Avtom/GRAM-PRISM/Arcade  v1/art/back.png

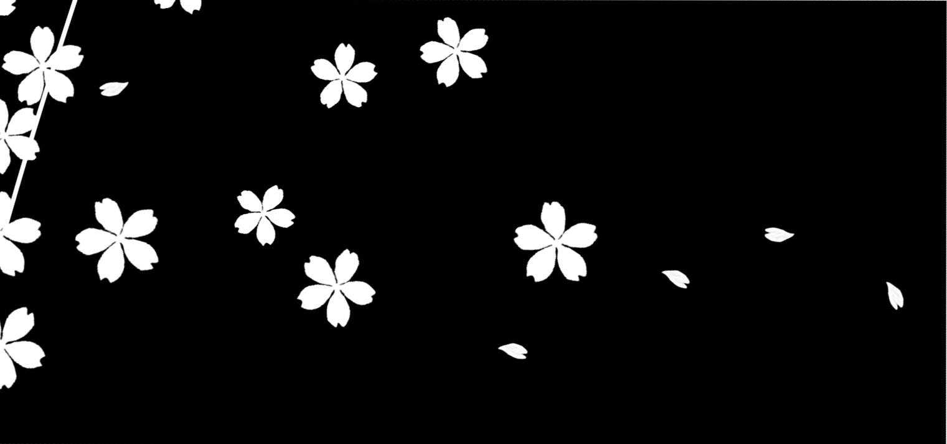
Arcade v1/art/back.png
