Avtom/GRAM-PRISM/Arcade  v1/art/front.png

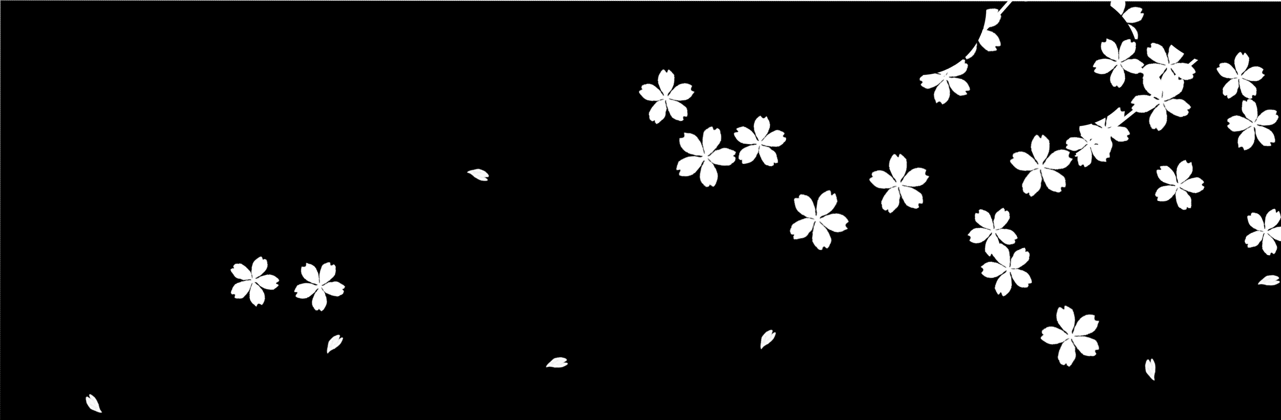
Arcade v1/art/front.png
