Avtom/GRAM-PRISM/Arcade  v1/art/left.png

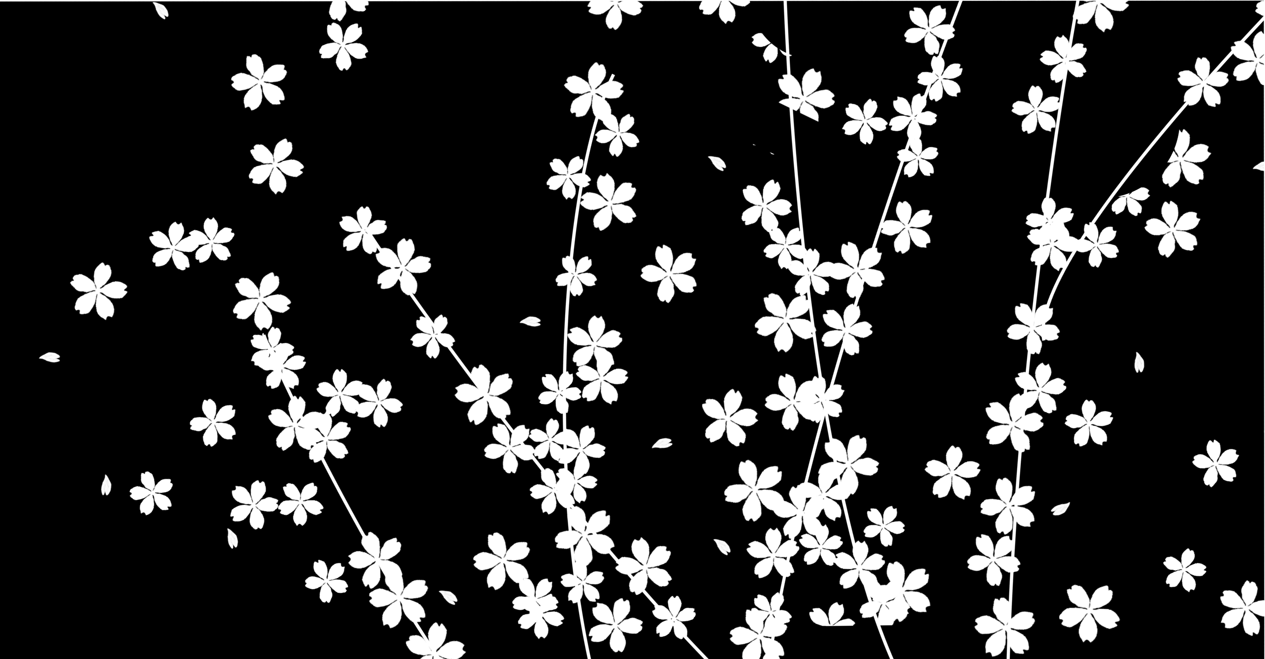
Arcade v1/art/left.png
