Avtom/GRAM-PRISM/Arcade  v1/art/right.png

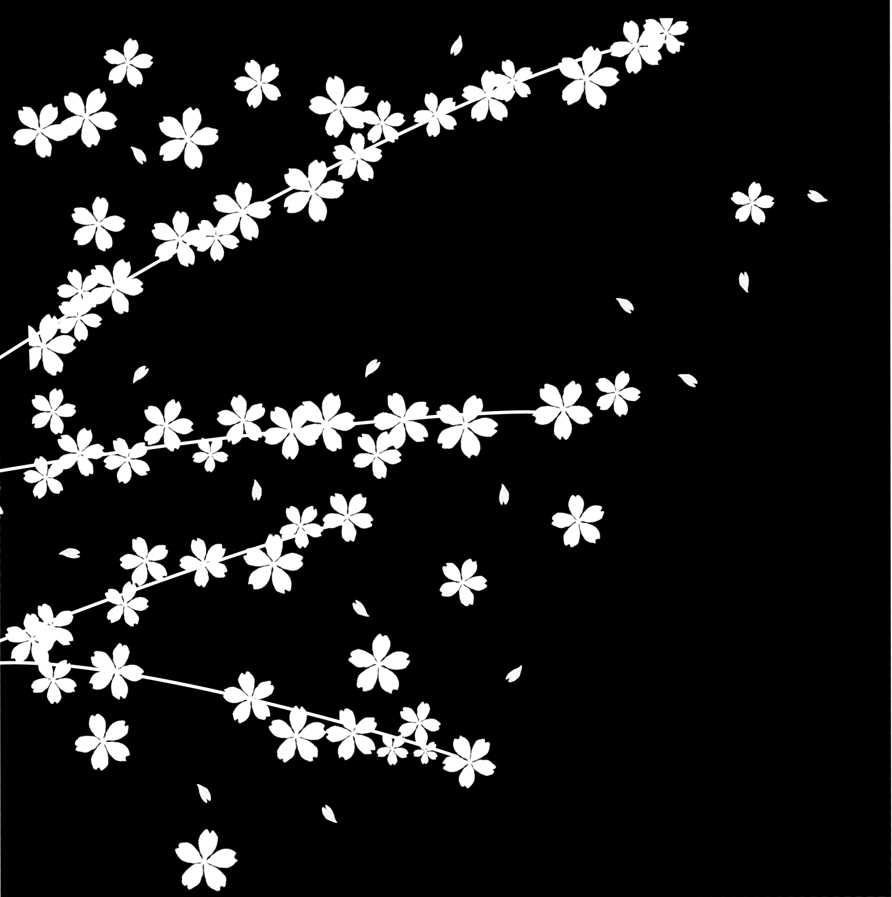
Arcade v1/art/right.png
