Avtom/GRAM-PRISM/Arcade  v1/documentation/arcade-2.jpg

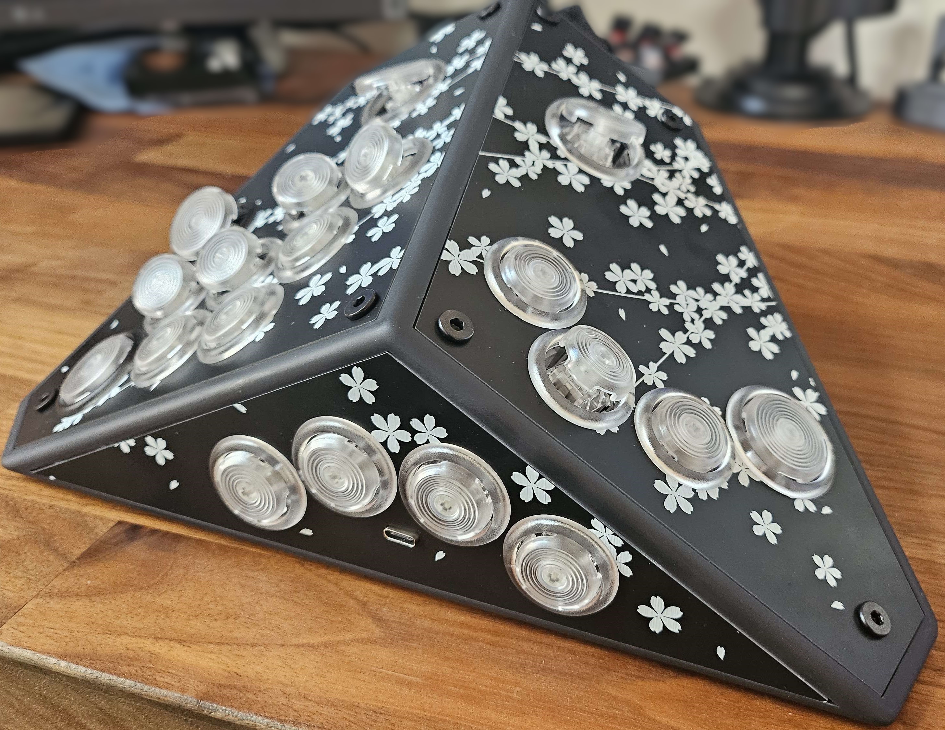
Arcade v1/documentation/arcade-2.jpg
