Avtom/GRAM-PRISM/Arcade  v1/documentation/arcade-3.jpg

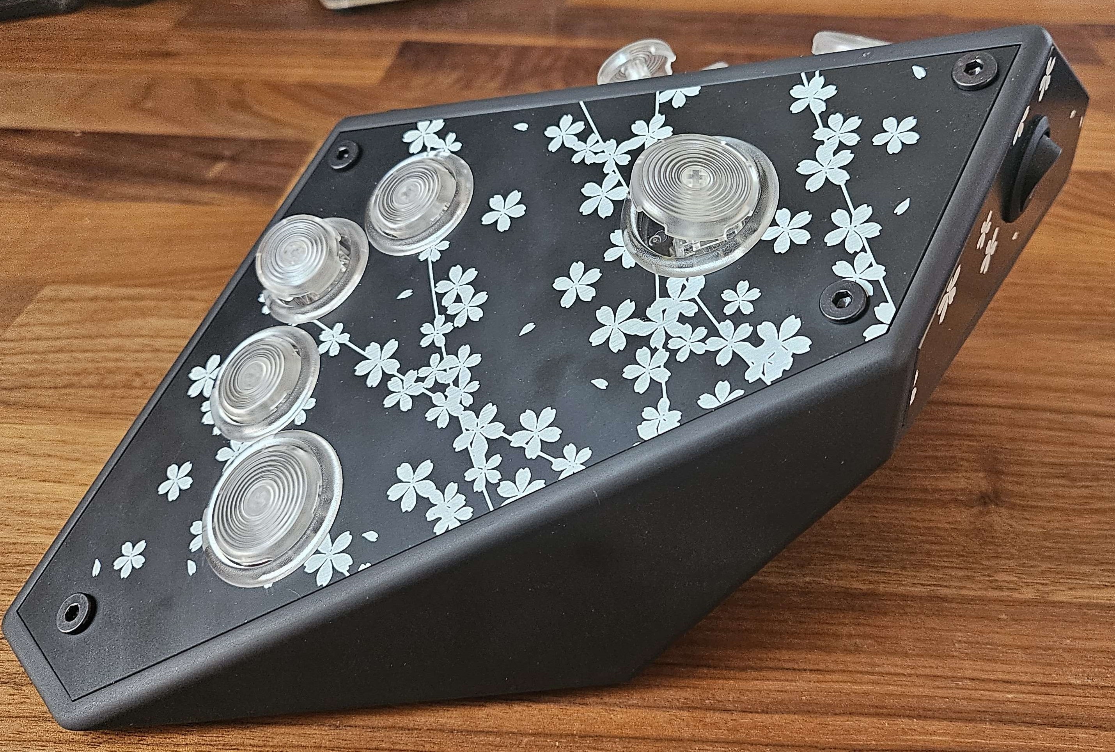
Arcade v1/documentation/arcade-3.jpg
