Avtom/GRAM-PRISM/Arcade  v1/documentation/arcade-4.jpg

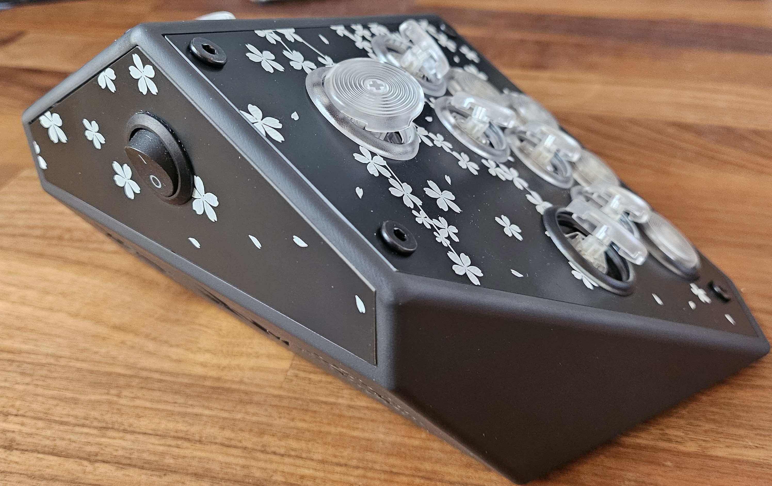
Arcade v1/documentation/arcade-4.jpg
