Avtom/GRAM-PRISM/Arcade  v1/documentation/arcade-5.jpg

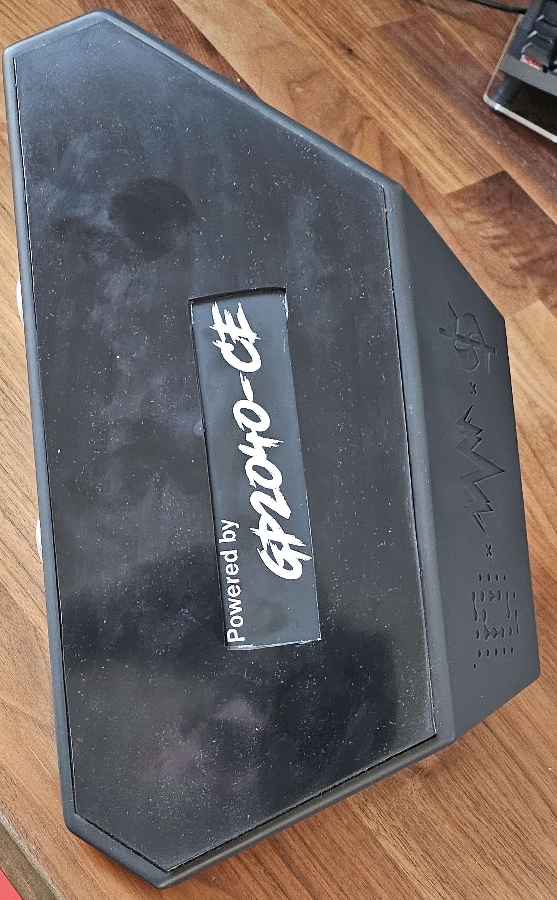
Arcade v1/documentation/arcade-5.jpg
