Avtom/GRAM-PRISM/Arcade  v1/documentation/arcade-6.jpg

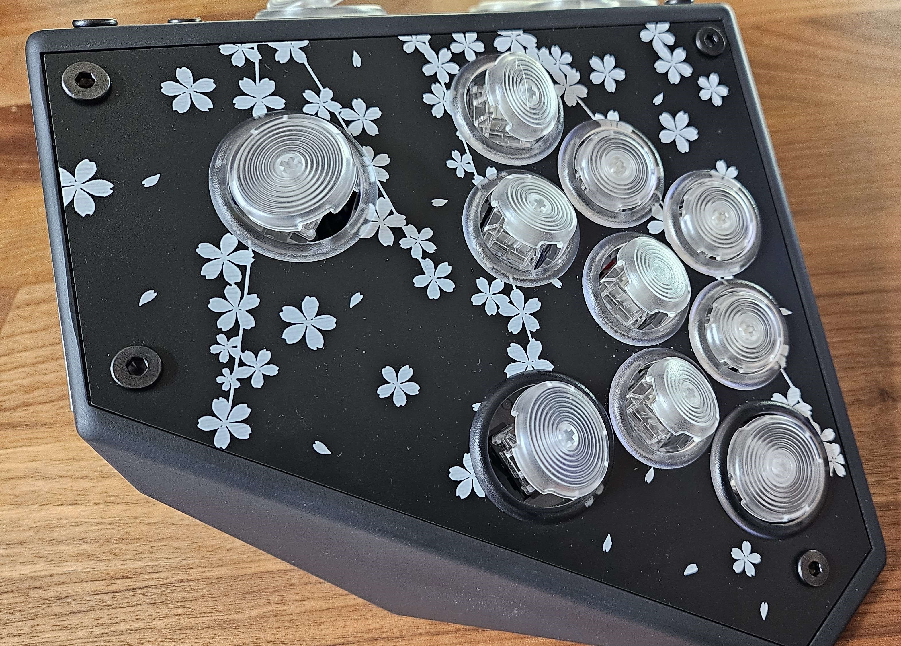
Arcade v1/documentation/arcade-6.jpg
