Avtom/GRAM-PRISM/Arcade  v1/documentation/arcade-7.jpg

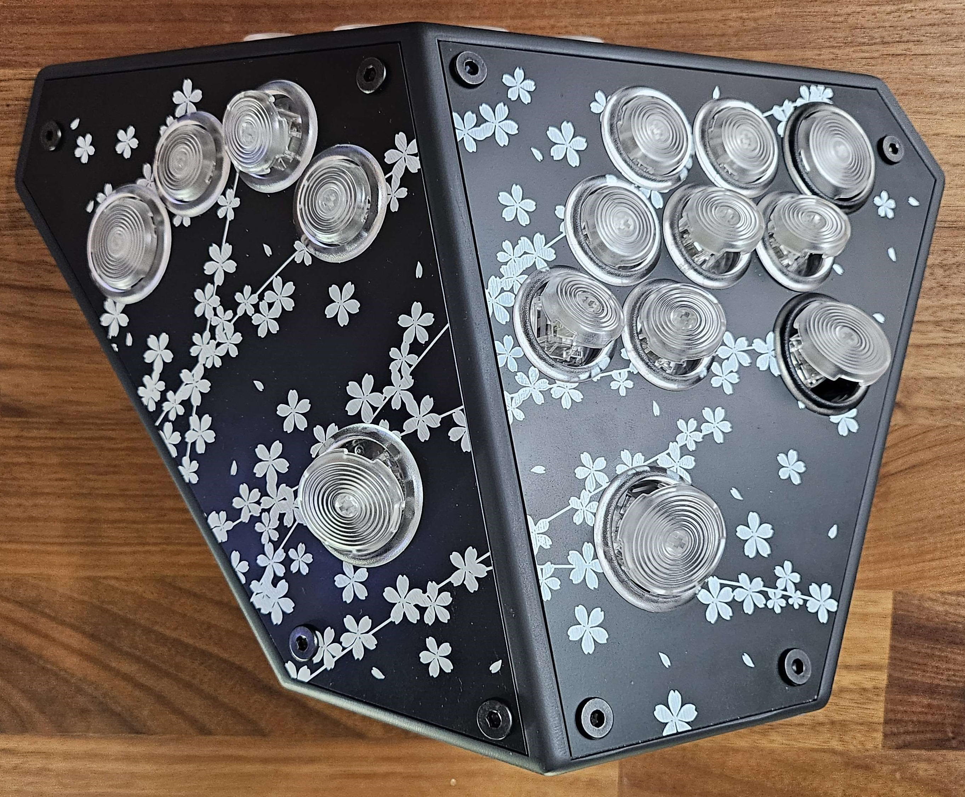
Arcade v1/documentation/arcade-7.jpg
