Avtom/GRAM-PRISM/Arcade  v1/documentation/arcade-notilters.jpg

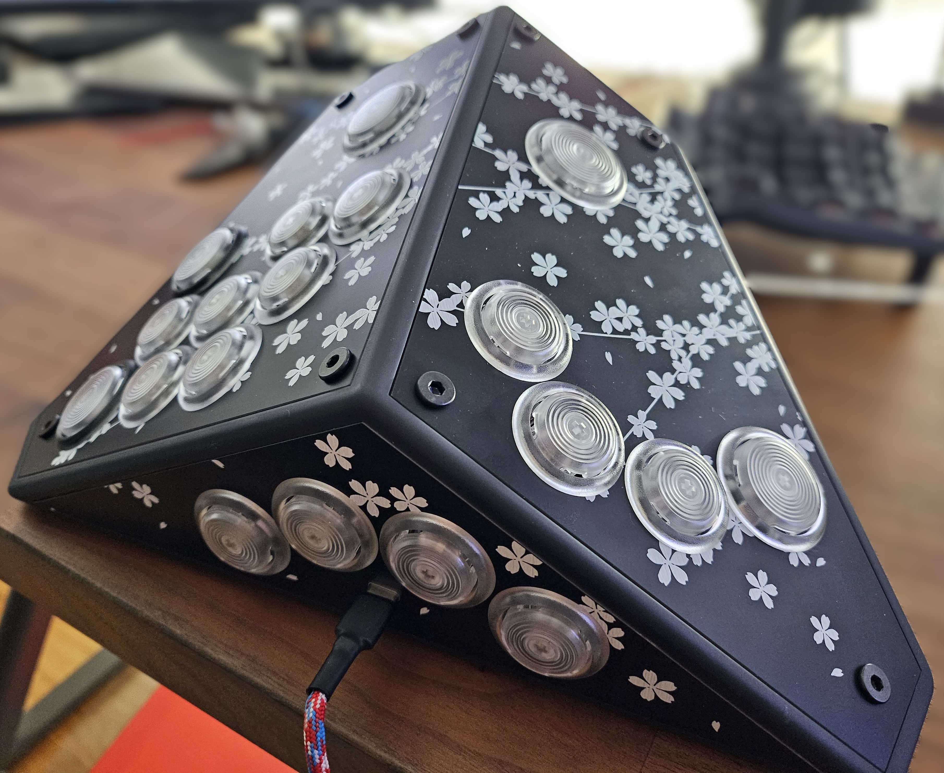
Arcade v1/documentation/arcade-notilters.jpg
