Avtom/GRAM-PRISM/Arcade  v1/documentation/without-button-2.jpg

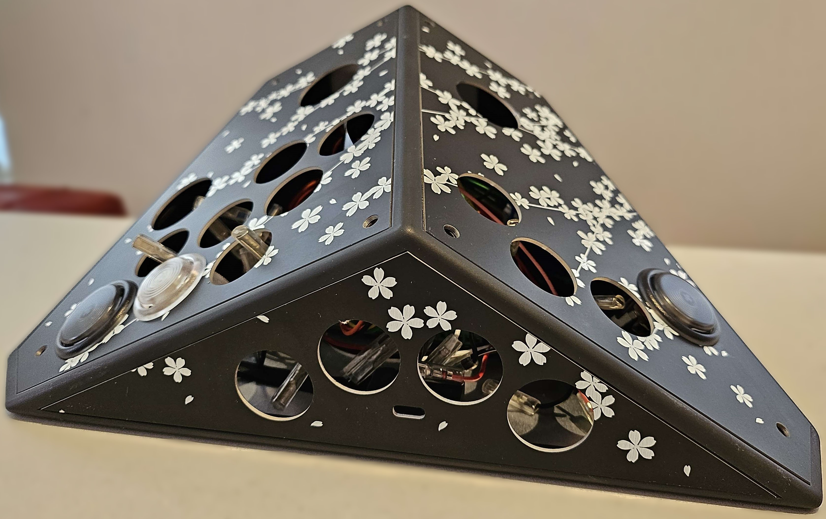
Arcade v1/documentation/without-button-2.jpg
