Avtom/GRAM-PRISM/Arcade  v1/stl/stl 2mm thick/right panel no aux buttons alt version v1.stl

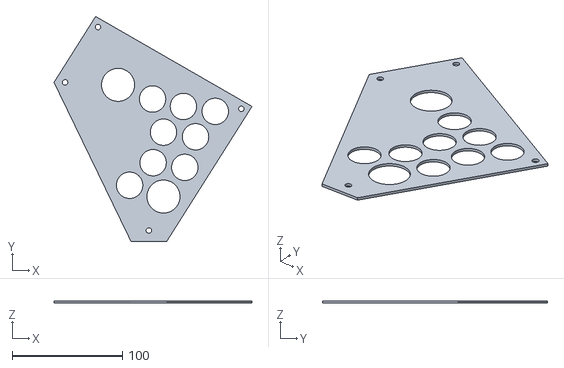
[picture p54: CAD file, 2024-02-25]
Arcade v1/stl/stl 2mm thick/right panel no aux buttons alt version v1.stl
179.7 x 204.3 x 2.00
