Avtom/GRAM-PRISM/Arcade  v1/dxf/left panel 16mm aux buttons.dxf

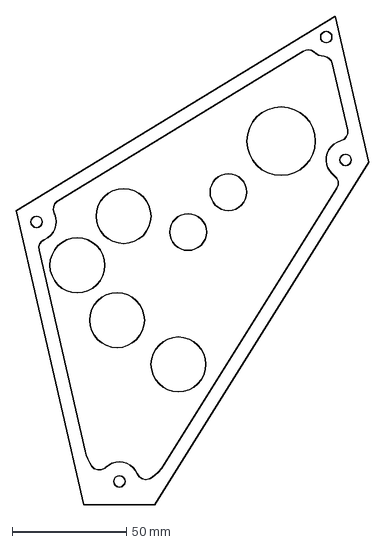
[picture p55: CAD file, 2024-02-10]
Arcade v1/dxf/left panel 16mm aux buttons.dxf
153.9 x 213.6 mm
