Avtom/GRAM-PRISM/Arcade  v1/stl/stl 2mm thick/bottom v1.stl

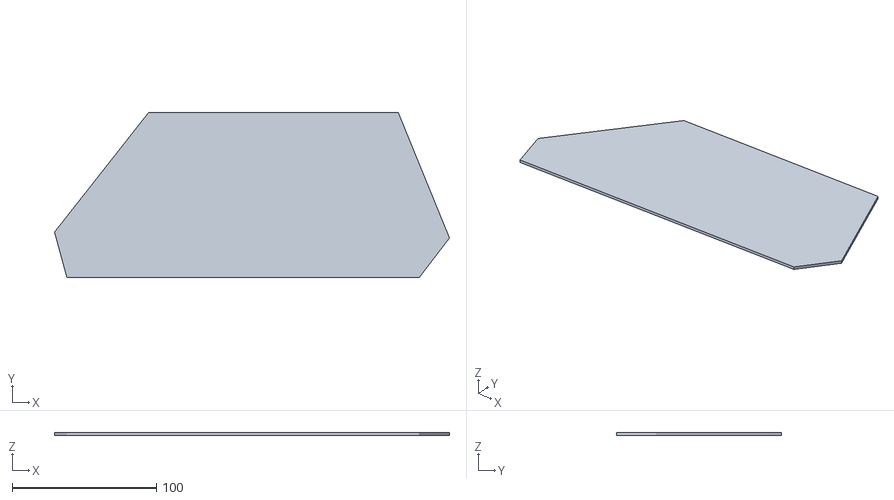
[picture p56: CAD file, 2024-02-25]
Arcade v1/stl/stl 2mm thick/bottom v1.stl
273.9 x 114.6 x 2.00
