Avtom/GRAM-PRISM/Arcade  v1/dxf/right panel 16mm aux buttons.dxf

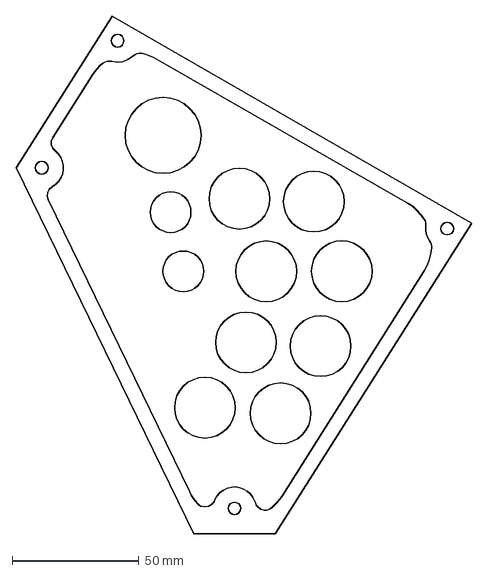
[picture p57: CAD file, 2024-02-10]
Arcade v1/dxf/right panel 16mm aux buttons.dxf
179.7 x 204.3 mm
