Avtom/GRAM-PRISM/Arcade  v1/stl/stl 2mm thick/smallest back with focus button v1.stl

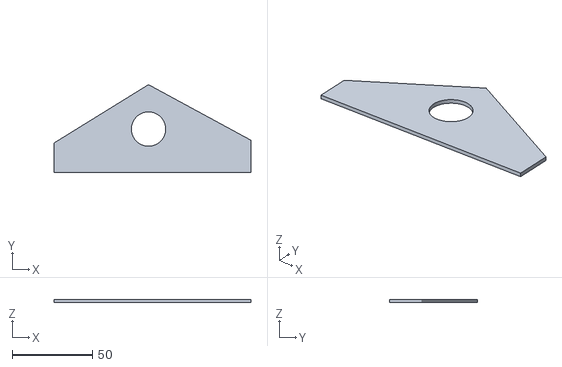
[picture p58: CAD file, 2024-02-25]
Arcade v1/stl/stl 2mm thick/smallest back with focus button v1.stl
122.6 x 54.6 x 2.00
