Avtom/GRAM-PRISM/Arcade  v1/stl/stl 2mm thick/front with port and 24mm Aux v1.stl

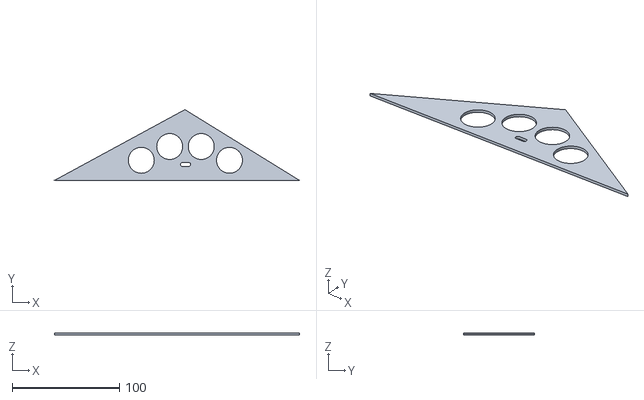
[picture p59: CAD file, 2024-02-18]
Arcade v1/stl/stl 2mm thick/front with port and 24mm Aux v1.stl
228.1 x 65.9 x 2.00
